richteel/SpeechTimer/Case/Laser Cut/Case/Main PCB.png

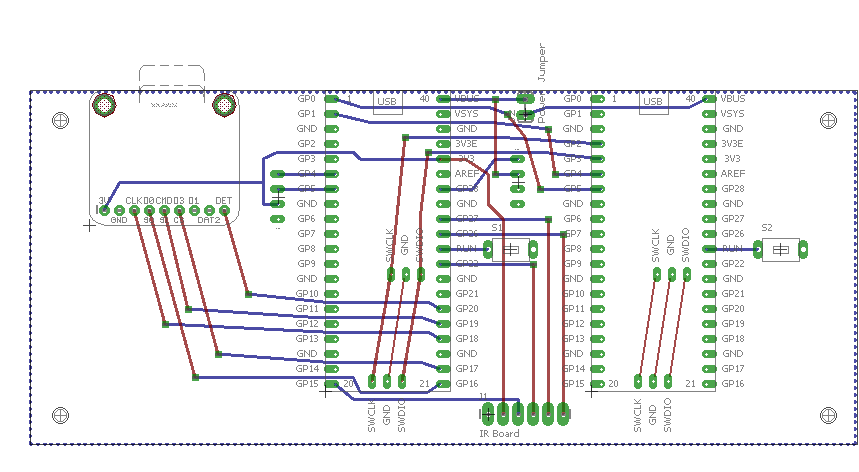
Case/Laser Cut/Case/Main PCB.png
