richteel/SpeechTimer/Case/Laser Cut/Case/Main PCB_flipped.png

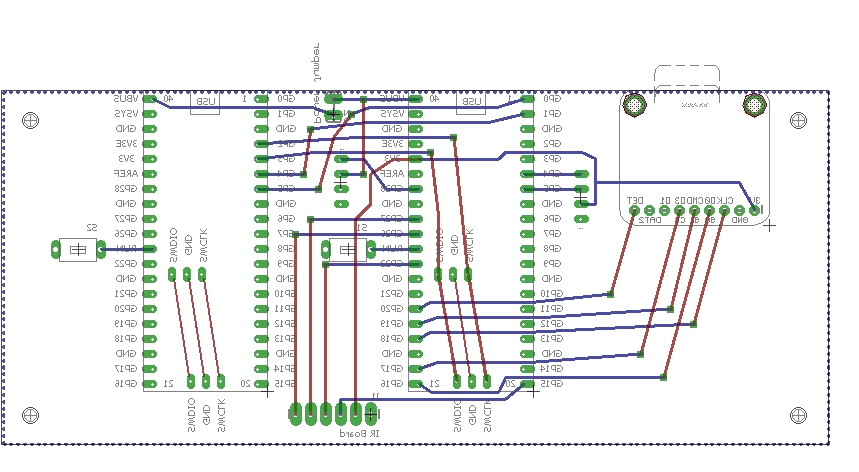
Case/Laser Cut/Case/Main PCB_flipped.png
