richteel/SpeechTimer/Case/Laser Cut/Case/PXL_20231123_190553922 - Copy.jpg

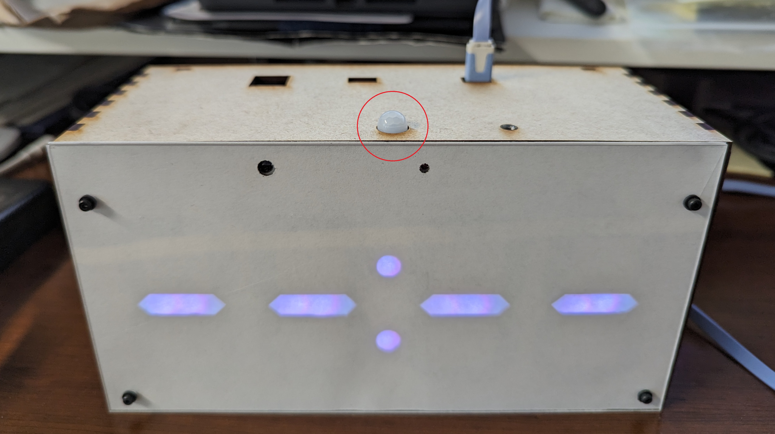
Case/Laser Cut/Case/PXL_20231123_190553922 - Copy.jpg
