richteel/SpeechTimer/Case/Laser Cut/Case/PXL_20231123_190553922.jpg

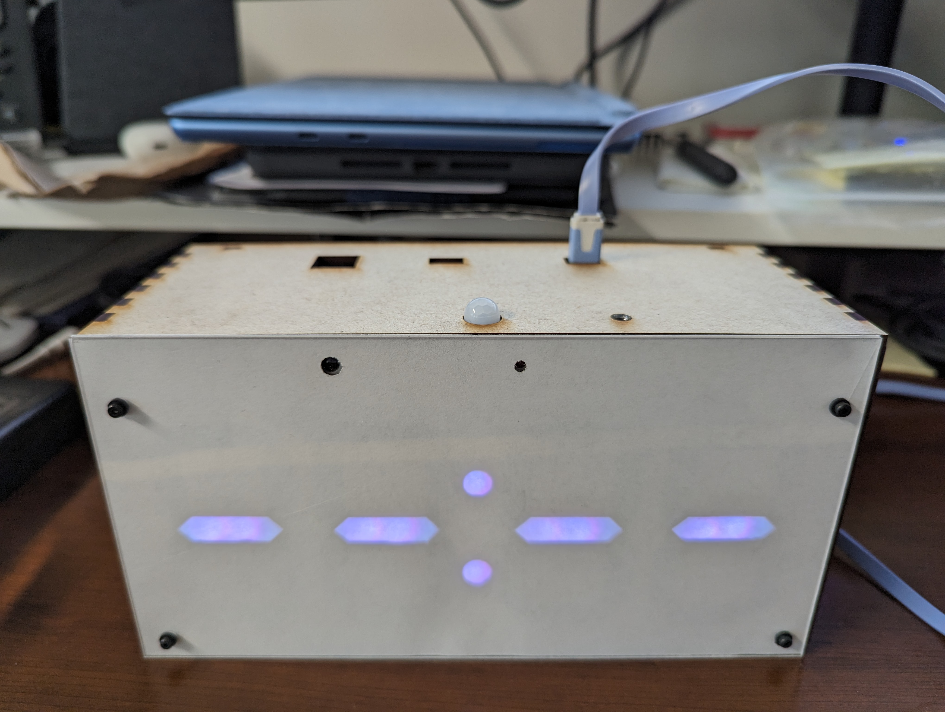
Case/Laser Cut/Case/PXL_20231123_190553922.jpg
