richteel/SpeechTimer/Case/Laser Cut/Case/PXL_20231123_191028927.MP - Copy.jpg

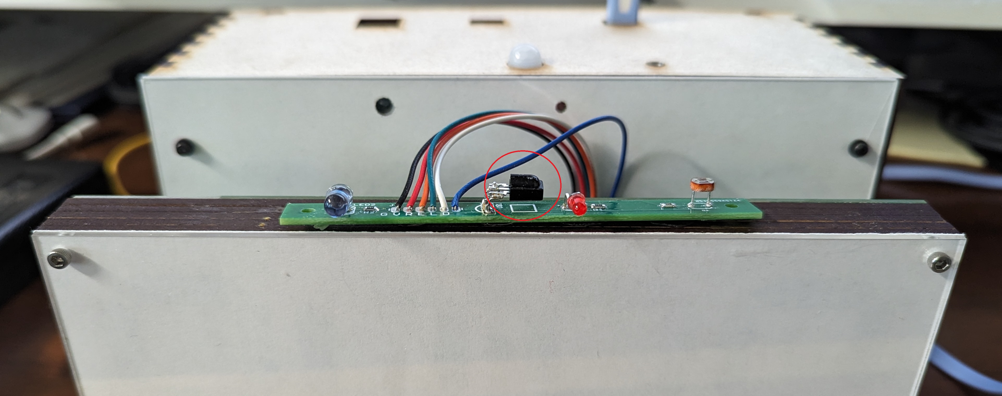
Case/Laser Cut/Case/PXL_20231123_191028927.MP - Copy.jpg
