richteel/SpeechTimer/Case/M2.5 Nut Drawing.png

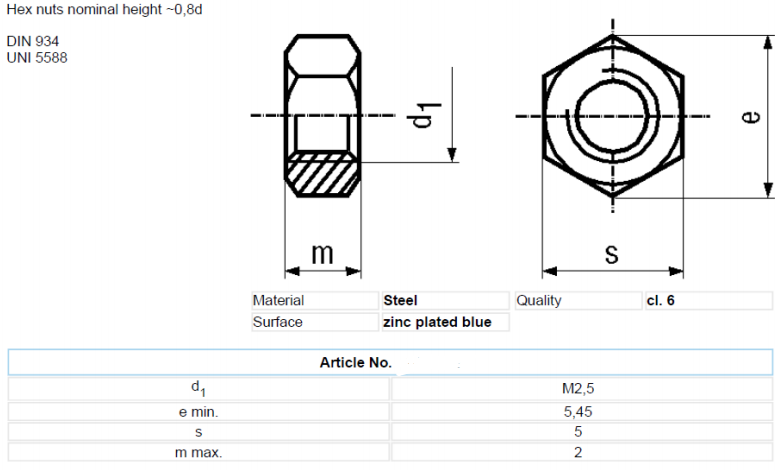
Case/M2.5 Nut Drawing.png
