richteel/SpeechTimer/Documentation/Datasheets/S66a6b27205ca4aaaa45f665b13f1ae5bm.webp

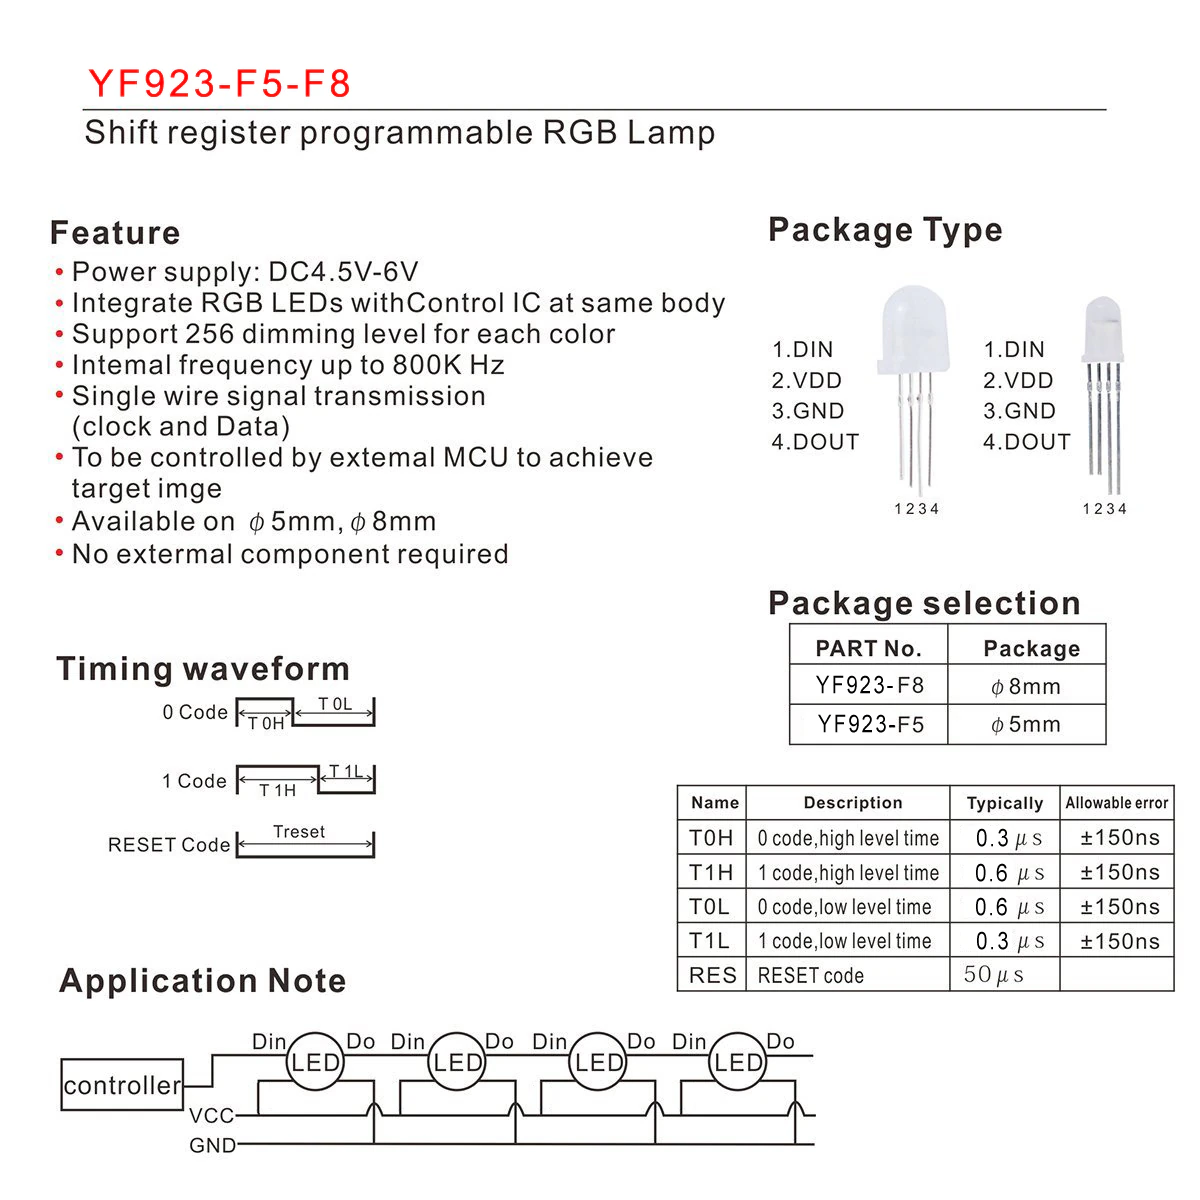
Documentation/Datasheets/S66a6b27205ca4aaaa45f665b13f1ae5bm.webp
