richteel/SpeechTimer/Documentation/Images/Front.jpg

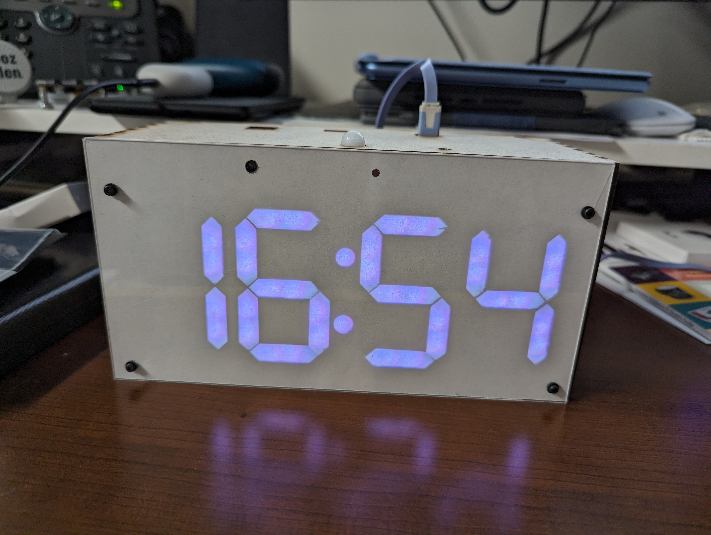
Documentation/Images/Front.jpg
