richteel/SpeechTimer/Documentation/Images/pico.png

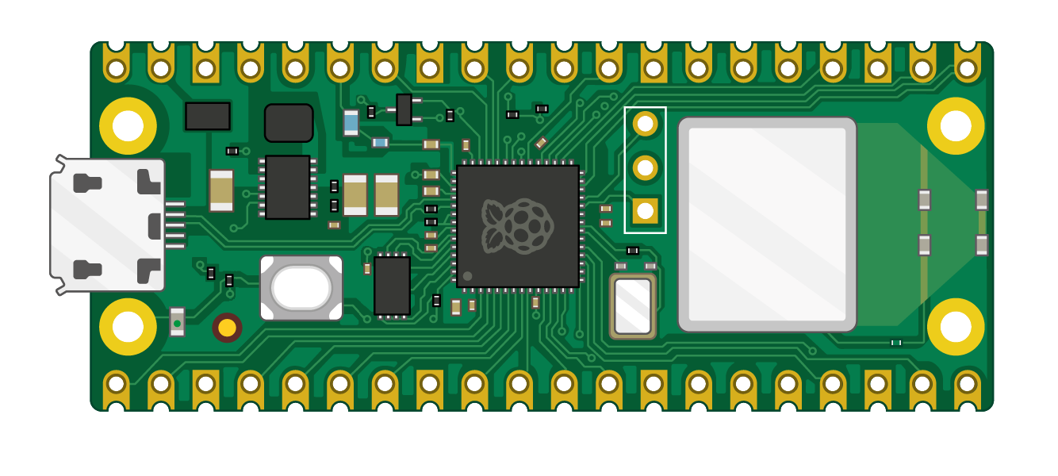
Documentation/Images/pico.png
