richteel/SpeechTimer/Documentation/Images/Remote.png

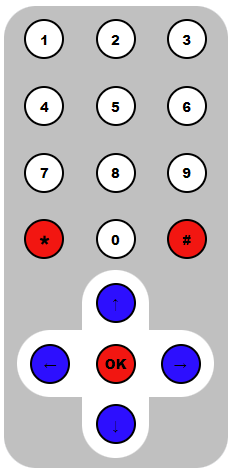
Documentation/Images/Remote.png
