richteel/SpeechTimer/SpeechTimer/Defines.h

#ifndef GLOBALDEFINES_H
#define GLOBALDEFINES_H

/*****************************************************************************
 *                           FreeRTOS Configuration                          *
 *****************************************************************************/
// Must be defined BEFORE any FreeRTOS headers are included
#if defined(ARDUINO_ARCH_MBED_RP2040) || defined(ARDUINO_ARCH_RP2040)
#define __FREERTOS 1
#endif

/*
  ** HW Device Connection on Raspberry Pi Pico W **
    Pin GPIO  Device  Device Pin/Function
    6   GP4   OLED      SDA
    7   GP5   OLED      SCK
    20  GP15  Indicator LED
    21  GP16  SD Card   MISO
    22  GP17  SD Card   CS
    24  GP18  SD Card   SCK
    25  GP19  SD Card   MOSI
    26  GP20  SD Card   CD
    29  GP22  IR LED
    31  GP26  IR Remote Signal
    32  GP27  Light Detector (CdS Photoresistor)
    34  GP28  NeoPixels Data
*/

// ***** Pins *****
#define NO_PIN 255

#define PIN_OLED_SDA 4
#define PIN_OLED_SCK 5

#define PIN_LED_INDICATOR 15

#define PIN_SDCARD_MISO 16
#define PIN_SDCARD_CS 17
#define PIN_SDCARD_SCK 18
#define PIN_SDCARD_MOSI 19
#define PIN_SDCARD_CD 20

#define PIN_LED_IR 22

#define PIN_DETECTOR_IR 26

#define PIN_DETECTOR_LIGHT 27  // 27  A1

#define PIN_NEOPIXEL_DATA 28

// ***** OLED SETTINGS *****
#define OLED_SCREEN_WIDTH 128  // OLED display width, in pixels
#define OLED_SCREEN_HEIGHT 32  // OLED display height, in pixels

// Declaration for an SSD1306 display connected to I2C (SDA, SCL pins)
// The pins for I2C are defined by the Wire-library.
// On an arduino UNO:       A4(SDA), A5(SCL)
// On an arduino MEGA 2560: 20(SDA), 21(SCL)
// On an arduino LEONARDO:   2(SDA),  3(SCL), ...
#define OLED_RESET -1             // Reset pin # (or -1 if sharing Arduino reset pin)
#define OLED_SCREEN_ADDRESS 0x3C  ///< See datasheet for Address; 0x3D for 128x64, 0x3C for 128x32
#define OLED_LINE_1_Y 2
#define OLED_LINE_2_Y 12  // 8
#define OLED_LINE_3_Y 22  // 16

// ***** NEOPIXEL CLOCK SETTINGS *****
#define NEOPIXEL_TOTAL_PIXELS 58
#define NEOPIXEL_TYPE NEO_RGB + NEO_KHZ800
#define NEOPIXEL_NUM_PER_SEGMENT 2
#define NEOPIXEL_NUM_DIGITS 4
#define NEOPIXEL_NUM_COLONS 2
#define NEOPIXEL_MAX_BRIGHTNESS 120  // Valid Values are 0 to 255
#define NEOPIXEL_MIN_BRIGHTNESS 5  // Valid Values are 0 to 255

// ***** FREERTOS TASK CONFIGURATION *****
// Task Stack Sizes (in words, not bytes)
#define TASK_STACK_SIZE 2048

// Task Delays (in milliseconds)
#define TASK_DELAY_SETUP_WAIT 10
#define TASK_DELAY_REMOTE_CHECK 250        // Fast polling for responsive remote control
#define TASK_DELAY_SDCARD_CHECK 500        // Slow polling - SD card changes are infrequent
#define TASK_DELAY_WIFI_CHECK_STABLE 1000  // Slow when WiFi is connected and stable
#define TASK_DELAY_WIFI_CHECK_UNSTABLE 250 // Fast when connecting or reconnecting
#define TASK_DELAY_CLOCK_UPDATE 100        // Fast for smooth display updates

// Queue Configuration
#define LOG_QUEUE_LENGTH 10
#define REMOTE_QUEUE_LENGTH 5

// Mutex Timeouts (in milliseconds)
#define MUTEX_TIMEOUT_MS 100
#define MUTEX_TIMEOUT_SHORT_MS 50
#define MUTEX_TIMEOUT_QUICK_MS 10

// Queue Send/Receive Timeouts (in milliseconds)
#define QUEUE_SEND_TIMEOUT_MS 10
#define QUEUE_RECEIVE_NO_WAIT 0

// Retry Configuration
#define MAX_SDCARD_WRITE_RETRIES 3
#define MAX_WIFI_CONNECT_ATTEMPTS 5
#define RETRY_DELAY_MS 25

// HTTP and RTC Configuration
#define HTTP_RESPONSE_BUFFER_SIZE 2048
#define HTTP_CONNECTION_RETRY_DELAY_MS 100

// Debug and Logging
#define LOOPS_BEFORE_TASK_INFO_PRINT 100


#endif  // GLOBALDEFINES_H
