richteel/SpeechTimer/CircuitPython/secrets.py

# SPDX-FileCopyrightText: 2020 Adafruit Industries
#
# SPDX-License-Identifier: Unlicense

# This file is where you keep secret settings, passwords, and tokens!
# If you put them in the code you risk committing that info or sharing it


secrets = {
    'ssid' : 'guest',
    'password' : 'password',
    'timezone' : "", # http://worldtimeapi.org/timezones
    }
